derui/Clairink/v1/case/case-v1_2.FCStd

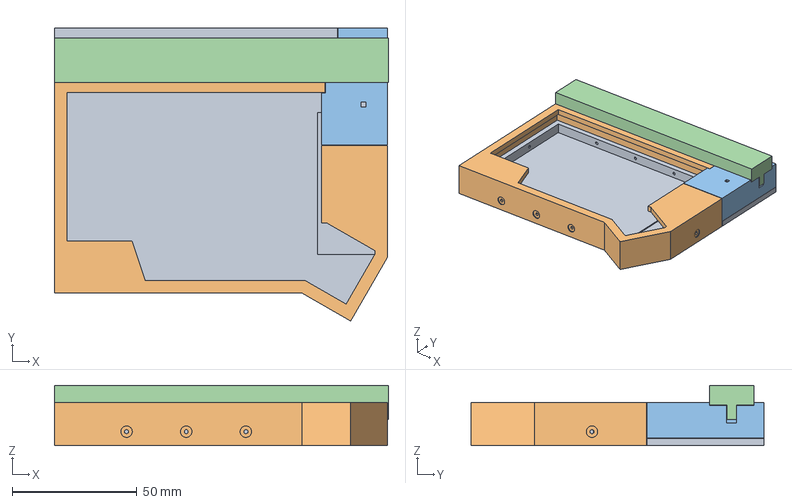
[picture p15: CAD file, 2026-05-13, an earlier design]
v1/case/case-v1_2.FCStd
134.1 x 117.7 x 24.3 mm
bottom
top
micom cover
battery cover
