derui/Clairink/v1/case/case-v1_2-finish.FCStd

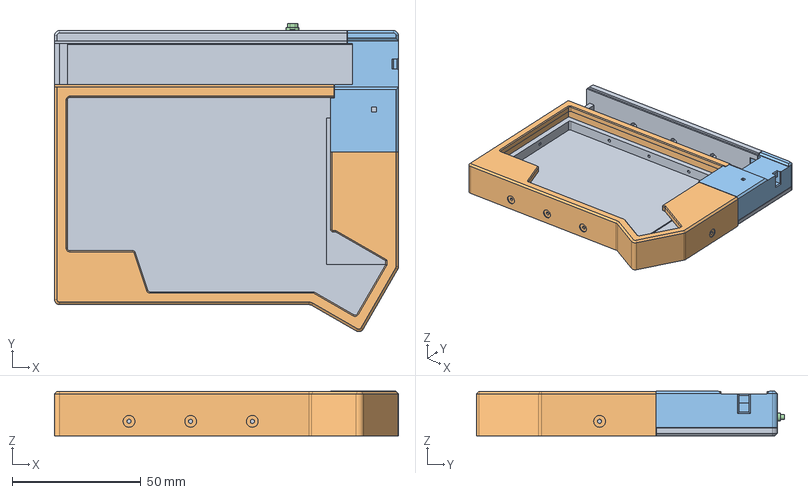
[picture p16: CAD file, 2026-05-13, an earlier design]
v1/case/case-v1_2-finish.FCStd
133.6 x 119.8 x 17.4 mm
bottom
top
micom cover
switch
